arunilkeshri/IoT-Based-Smart-Medicine-Dispenser/Docs/images/6233112915599280718.jpg

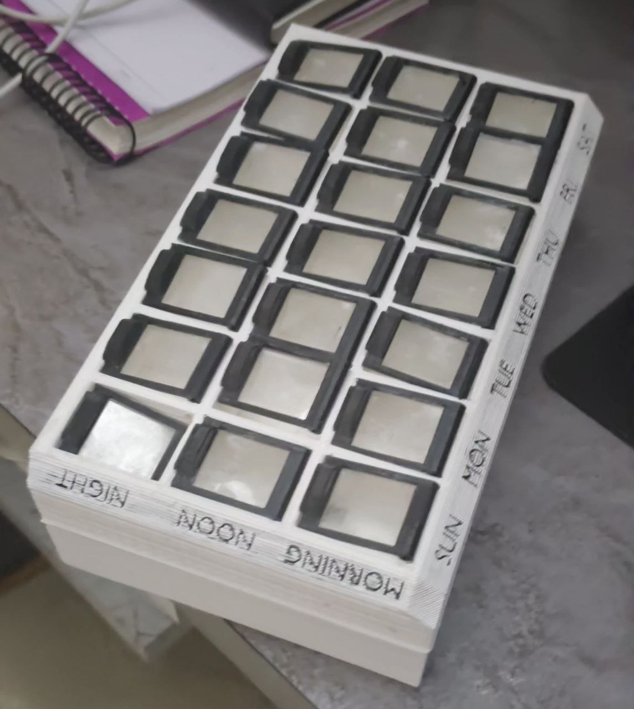
Docs/images/6233112915599280718.jpg
