arunilkeshri/IoT-Based-Smart-Medicine-Dispenser/Docs/images/6233112915599280722.jpg

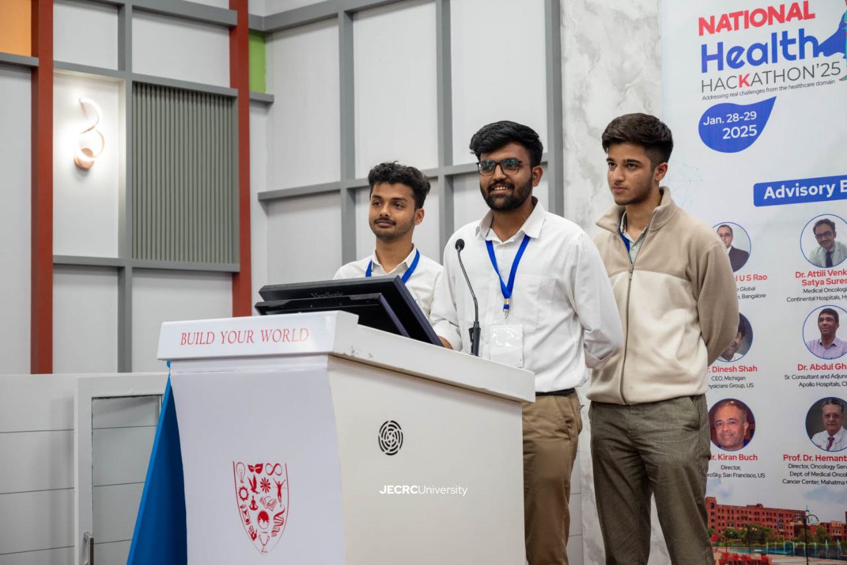
Docs/images/6233112915599280722.jpg
