arunilkeshri/IoT-Based-Smart-Medicine-Dispenser/Docs/images/6233112915599280723.jpg

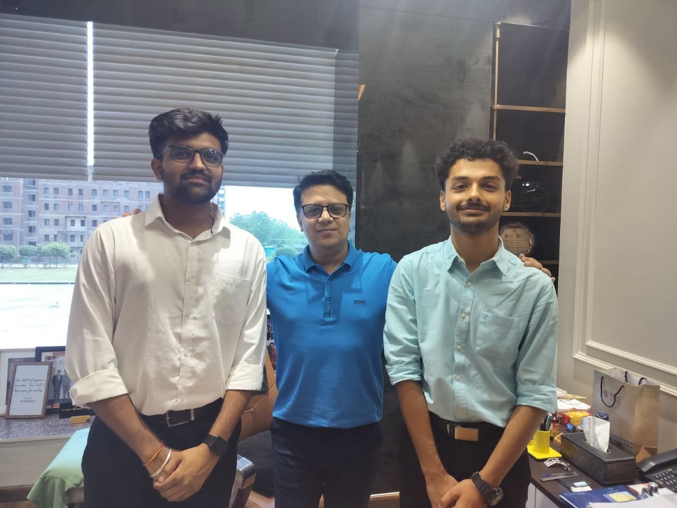
Docs/images/6233112915599280723.jpg
