arunilkeshri/IoT-Based-Smart-Medicine-Dispenser/Docs/raw/code png.png

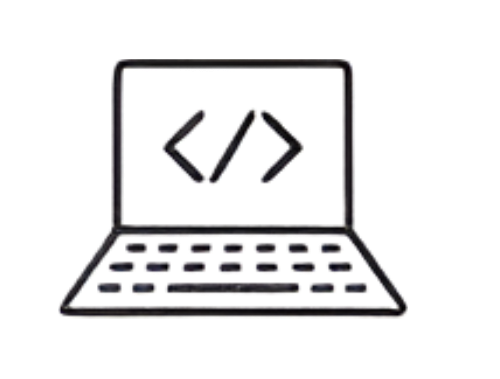
Docs/raw/code png.png
