arunilkeshri/IoT-Based-Smart-Medicine-Dispenser/Docs/raw/NHH PIC 1.png

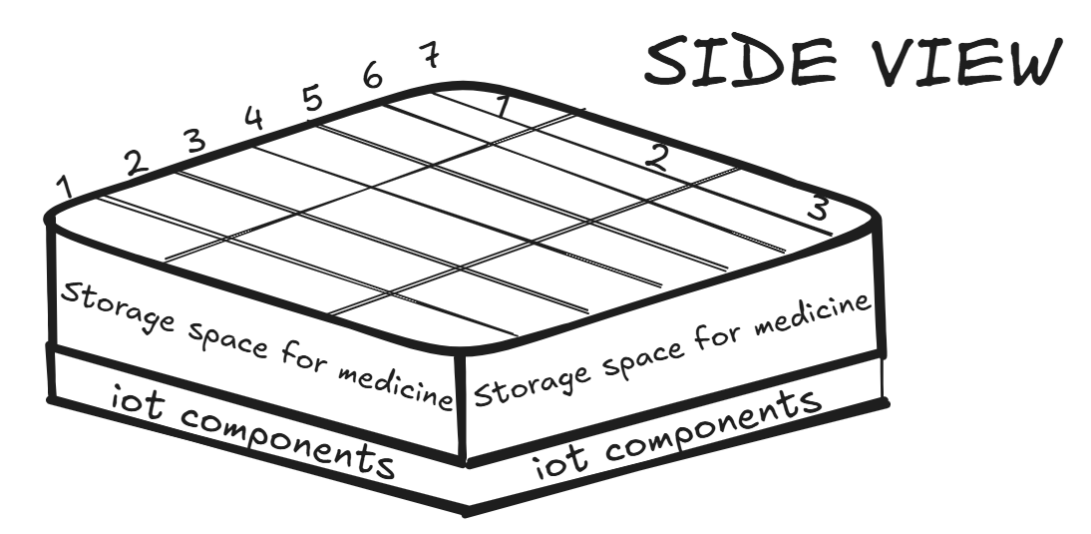
Docs/raw/NHH PIC 1.png
