arunilkeshri/IoT-Based-Smart-Medicine-Dispenser/Docs/raw/NHH PIC 2.png

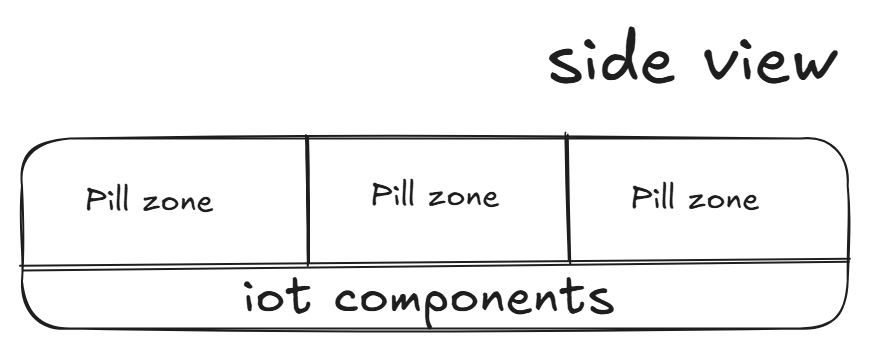
Docs/raw/NHH PIC 2.png
