arunilkeshri/IoT-Based-Smart-Medicine-Dispenser/Docs/raw/NHH PIC 3.png

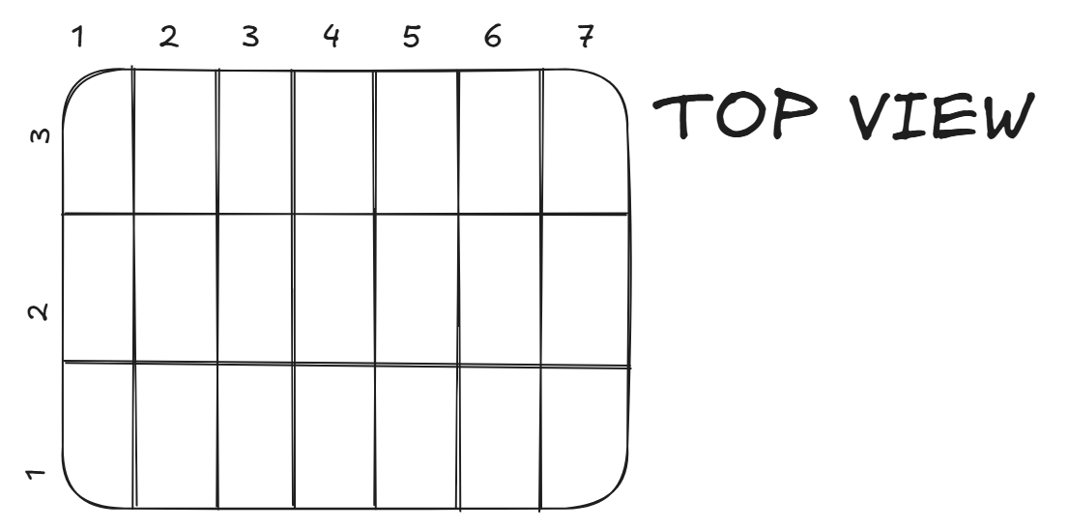
Docs/raw/NHH PIC 3.png
