arunilkeshri/IoT-Based-Smart-Medicine-Dispenser/Docs/raw/NHH PIC 4.png

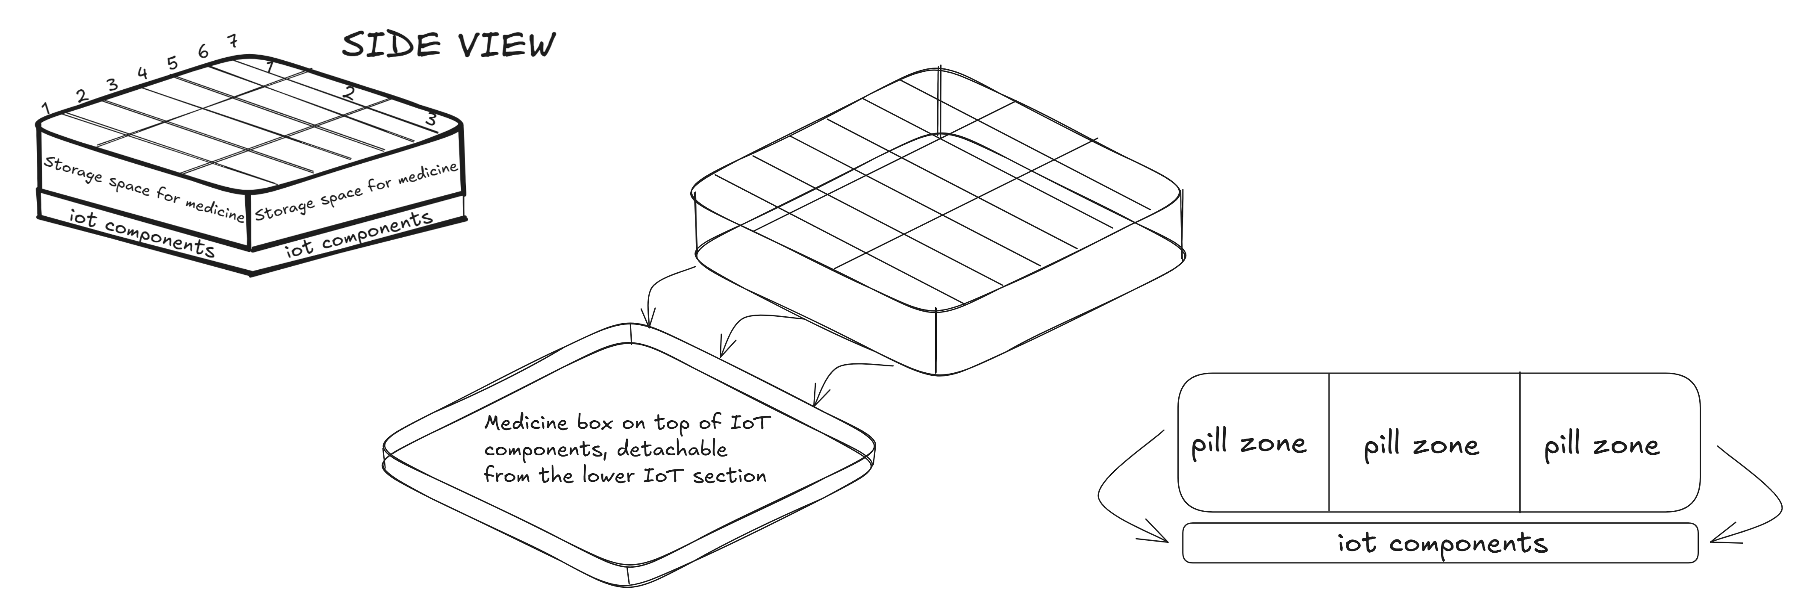
Docs/raw/NHH PIC 4.png
