arunilkeshri/IoT-Based-Smart-Medicine-Dispenser/Firmware/config.h

#ifndef CONFIG_H
#define CONFIG_H

// Wi-Fi credentials
#define WIFI_SSID "YourWiFiSSID"
#define WIFI_PASS "YourWiFiPassword"

// Blynk authentication token
#define BLYNK_AUTH "YourBlynkAuthToken"

// Telegram Bot credentials
#define TELEGRAM_BOT_TOKEN "YourTelegramBotToken"
#define TELEGRAM_CHAT_ID "YourChatID"

#endif
